uf-robopi/CavePI_AUV/CAD_designs/Computational Enclosure/Pixhawk.SLDPRT

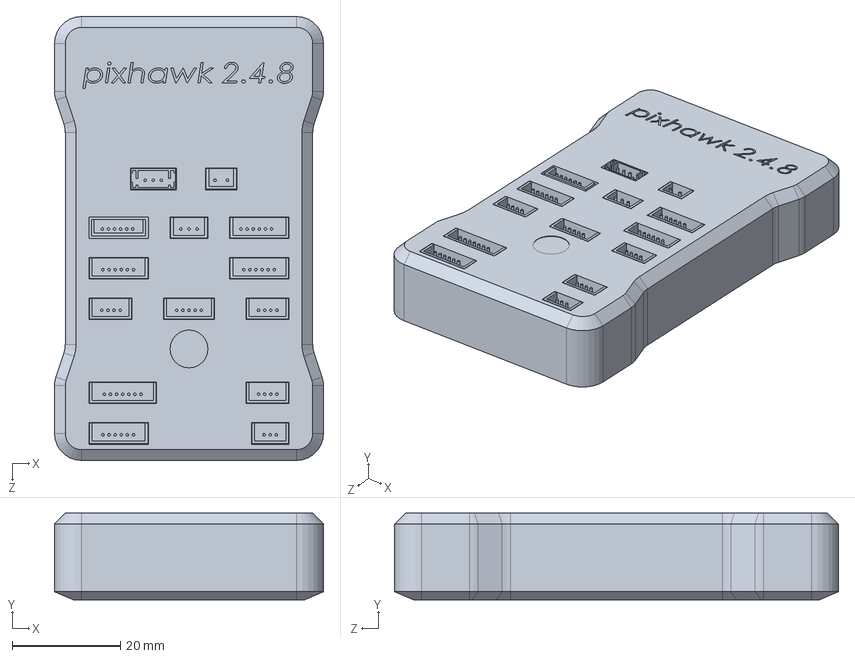
[picture p18: CAD file, 2025-04-15]
CAD_designs/Computational Enclosure/Pixhawk.SLDPRT
49.7 x 16.0 x 82.0 mm
