uf-robopi/CavePI_AUV/CAD_designs/Thrusters, Sonar, Lights, and Weights/Light.SLDPRT

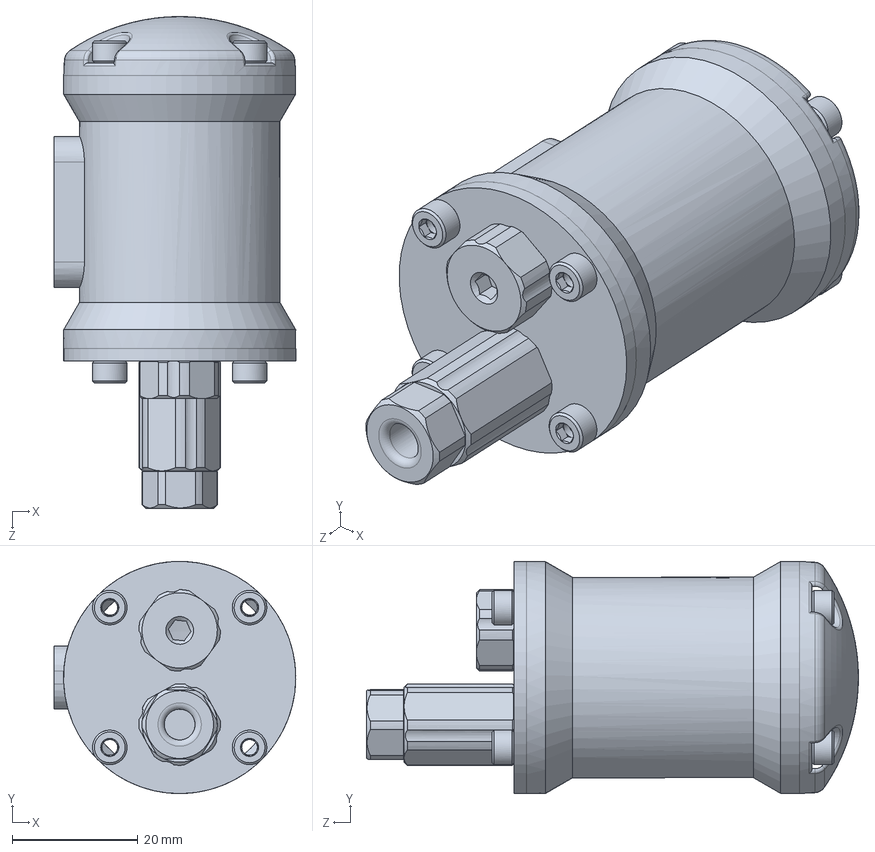
[picture p19: CAD file, 2025-04-15]
CAD_designs/Thrusters, Sonar, Lights, and Weights/Light.SLDPRT
38.5 x 37.0 x 78.4 mm
