uf-robopi/CavePI_AUV/CAD_designs/Computational Enclosure/Battery Mounting_Circular Plate.SLDPRT

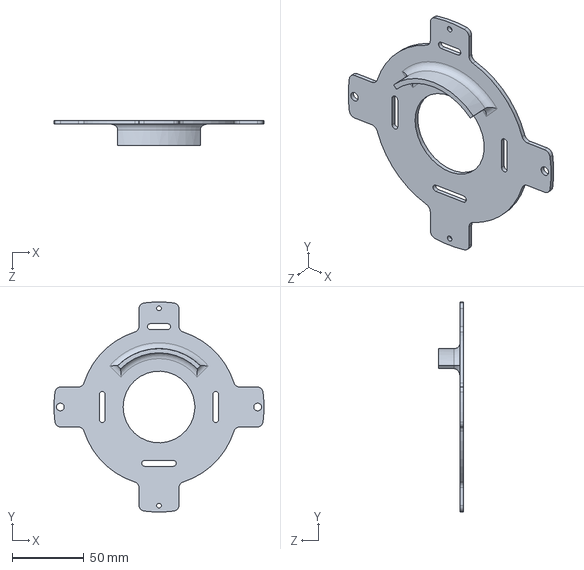
[picture p20: CAD file, 2025-04-15]
CAD_designs/Computational Enclosure/Battery Mounting_Circular Plate.SLDPRT
146.5 x 146.5 x 17.5 mm
