uf-robopi/CavePI_AUV/CAD_designs/Thrusters, Sonar, Lights, and Weights/Ballast Weight.SLDPRT

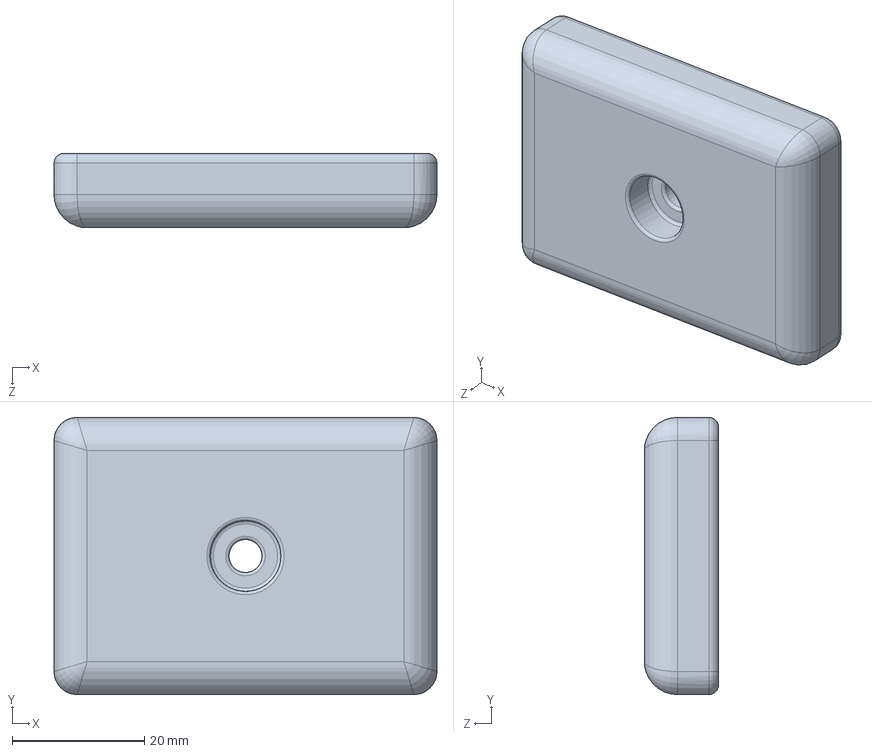
[picture p21: CAD file, 2025-04-15]
CAD_designs/Thrusters, Sonar, Lights, and Weights/Ballast Weight.SLDPRT
57.9 x 41.9 x 11.2 mm
