uf-robopi/CavePI_AUV/CAD_designs/Computational Enclosure/End Cap.SLDPRT

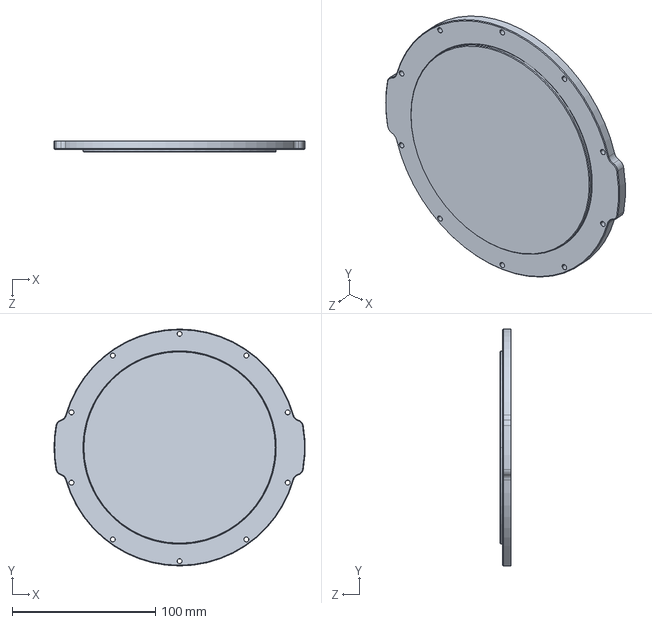
[picture p22: CAD file, 2025-04-15]
CAD_designs/Computational Enclosure/End Cap.SLDPRT
175.3 x 165.4 x 8.00 mm
