uf-robopi/CavePI_AUV/CAD_designs/Computational Enclosure/Battery Mounting_Bottom Plate.SLDPRT

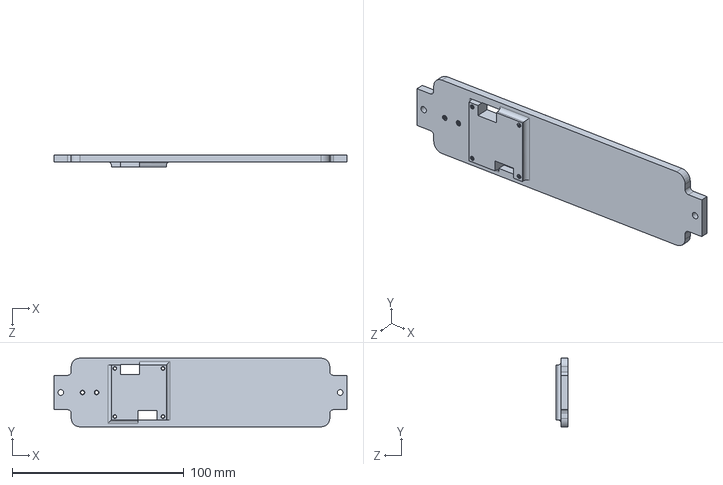
[picture p23: CAD file, 2025-04-15]
CAD_designs/Computational Enclosure/Battery Mounting_Bottom Plate.SLDPRT
170.5 x 40.0 x 7.01 mm
