uf-robopi/CavePI_AUV/CAD_designs/Computational Enclosure/Basic ESC.SLDPRT

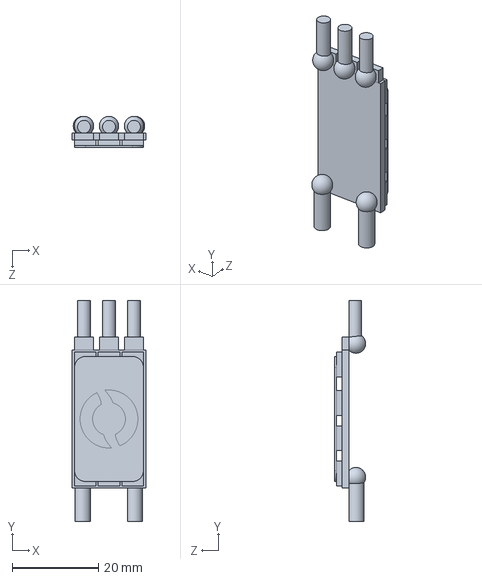
[picture p24: CAD file, 2025-04-15]
CAD_designs/Computational Enclosure/Basic ESC.SLDPRT
17.1 x 51.3 x 7.28 mm
