uf-robopi/CavePI_AUV/CAD_designs/Computational Enclosure/Tether Interface Module.SLDPRT

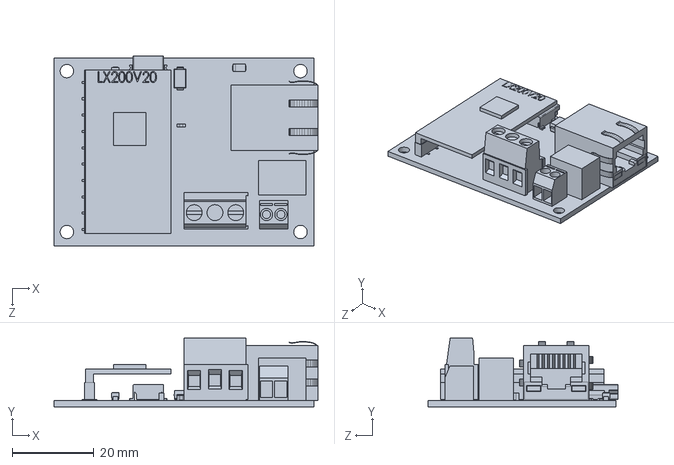
[picture p25: CAD file, 2025-04-15]
CAD_designs/Computational Enclosure/Tether Interface Module.SLDPRT
64.6 x 16.8 x 46.6 mm
