uf-robopi/CavePI_AUV/CAD_designs/Computational Enclosure/Battery Junction.SLDPRT

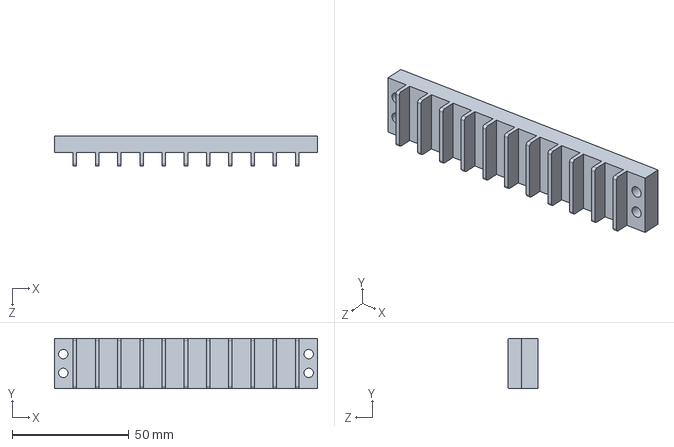
[picture p26: CAD file, 2025-04-15]
CAD_designs/Computational Enclosure/Battery Junction.SLDPRT
112.5 x 21.6 x 13.0 mm
