uf-robopi/CavePI_AUV/CAD_designs/Computational Enclosure/Euro Terminal Strip.SLDPRT

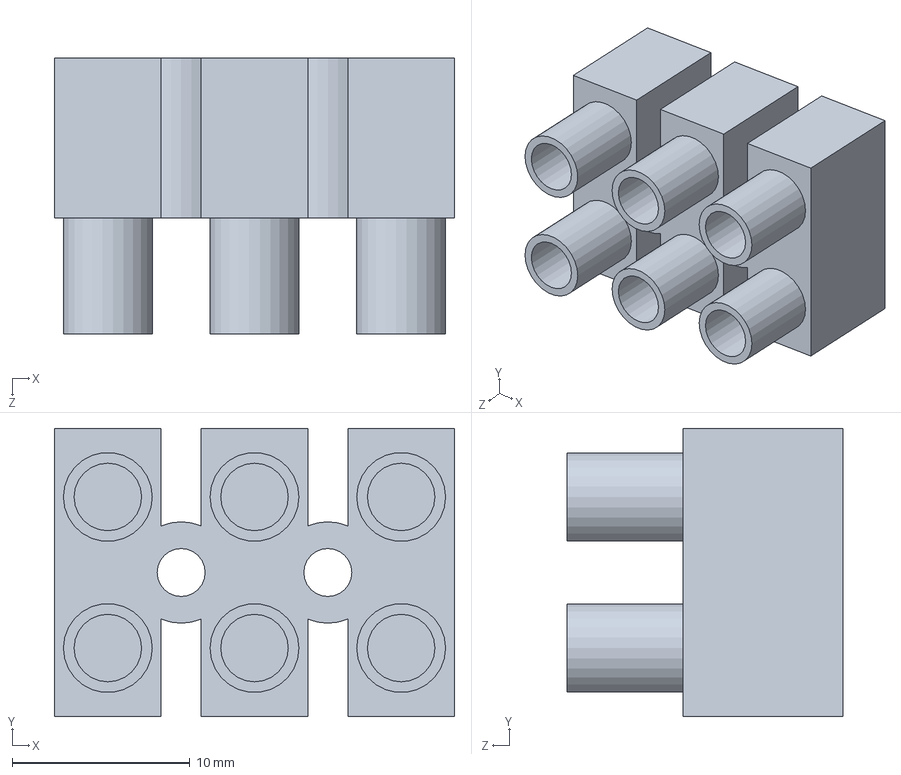
[picture p27: CAD file, 2025-04-15]
CAD_designs/Computational Enclosure/Euro Terminal Strip.SLDPRT
22.5 x 16.2 x 15.5 mm
