uf-robopi/CavePI_AUV/CAD_designs/Computational Enclosure/Tube.SLDPRT

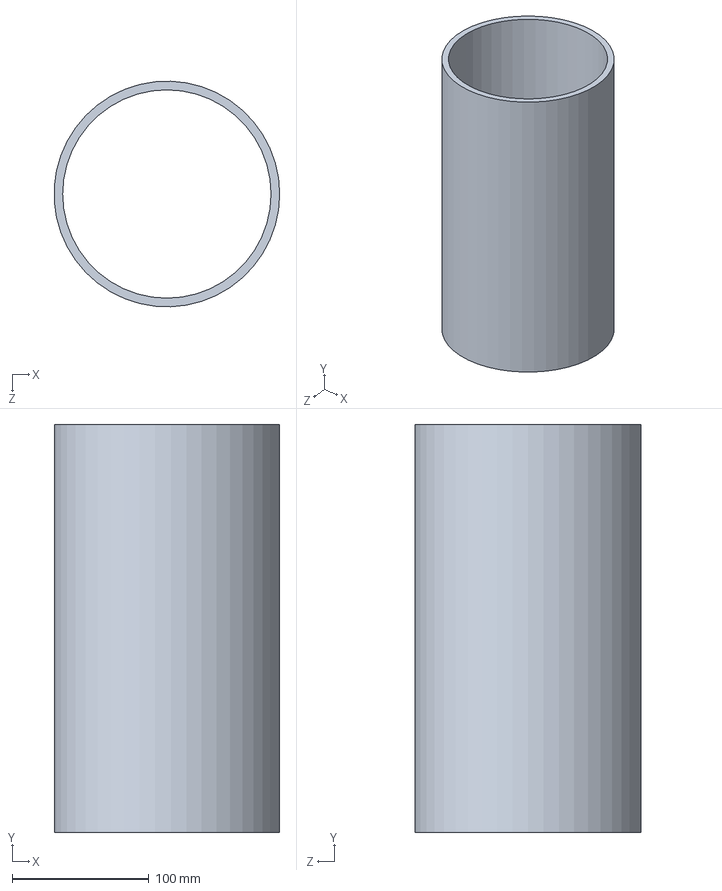
[picture p28: CAD file, 2025-04-15]
CAD_designs/Computational Enclosure/Tube.SLDPRT
164.9 x 298.4 x 165.0 mm
