uf-robopi/CavePI_AUV/CAD_designs/Computational Enclosure/Battery Mounting_Left Plate.SLDPRT

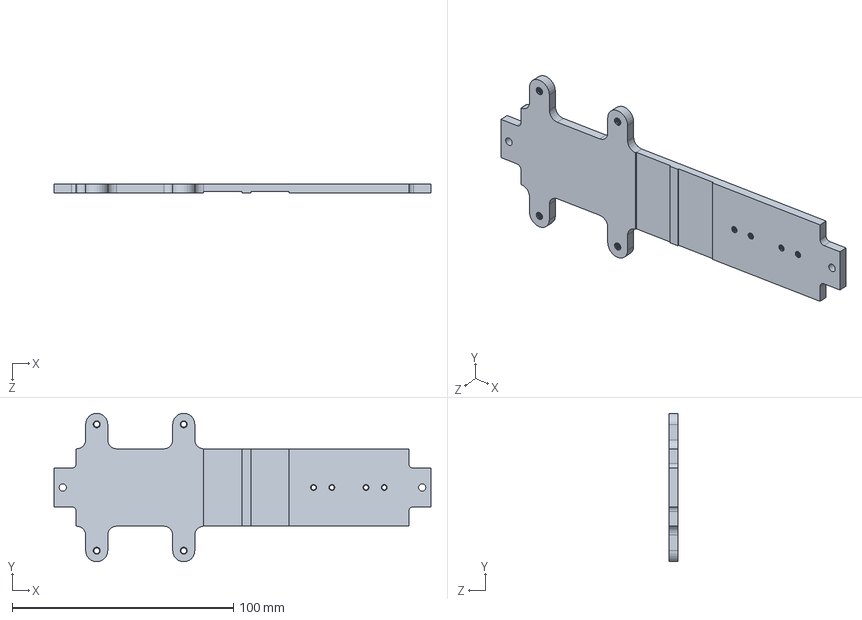
[picture p29: CAD file, 2025-04-15]
CAD_designs/Computational Enclosure/Battery Mounting_Left Plate.SLDPRT
170.5 x 67.1 x 3.90 mm
