uf-robopi/CavePI_AUV/CAD_designs/Computational Enclosure/Camera_Low Light.SLDPRT

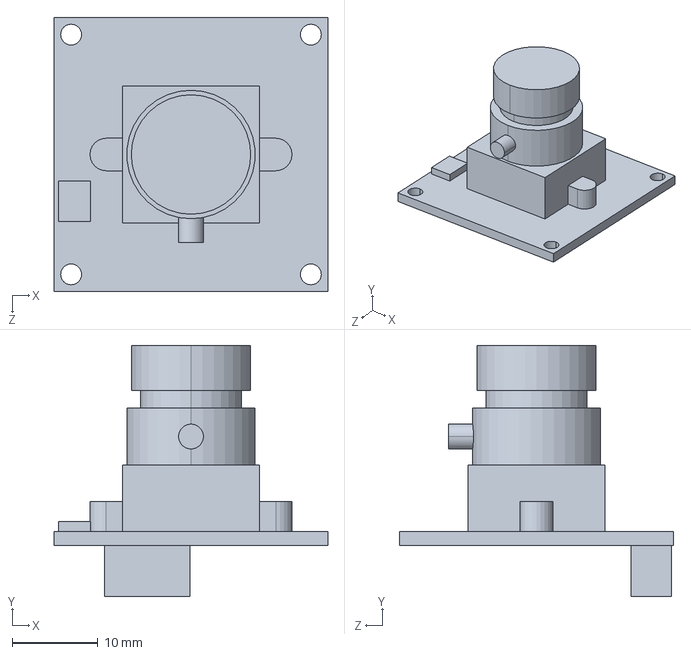
[picture p30: CAD file, 2025-04-15]
CAD_designs/Computational Enclosure/Camera_Low Light.SLDPRT
32.0 x 29.4 x 32.0 mm
