uf-robopi/CavePI_AUV/CAD_designs/Computational Enclosure/Raspberry Pi 5.SLDASM

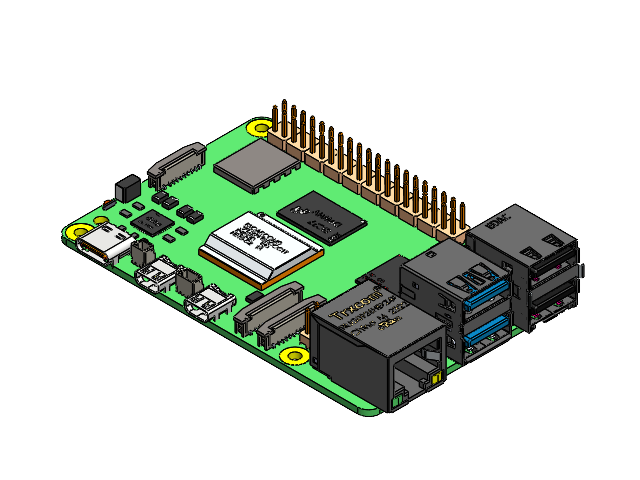
[picture p31: CAD file, 2025-04-15]
CAD_designs/Computational Enclosure/Raspberry Pi 5.SLDASM
PLATE_RASPBERRY_PI_5
METAL_PLATE.
GIGABIT_ETHERNET_PORT
2xUSB_3.0_PORT
2xUSB_2.0_PORT
FEMALE_MICRO_HDMI_CONNECTOR x 2
FEMALE_USB_CONNECTOR
STOCK_1
STOCK_2
STOCK_3
3.0_PIN_HEADER_10
2.0_PIN_HEADER
9FD77_D9WHV
GIGABIT_ETHERNET_TRANSCEIVER
RP1_CO_CONTROLLER
CARD_SLOT_METAL_PIN
SD_CARD_V1
PART3_V1
BROADCOM_1
MxL
CAMERA_DISPLAY_1
BUTTON_MINI
BUTTON_2
CONNECT_V1
CAMERA_DISPLAY_2 x 2
